unam-transients/tequila/hardware/Edmund Optics/39038/curv_39038.pdf

## 550 - 750nm, λ/4 Achromatic Waveplate Typical Retardance

## FOR REFERENCE ONLY

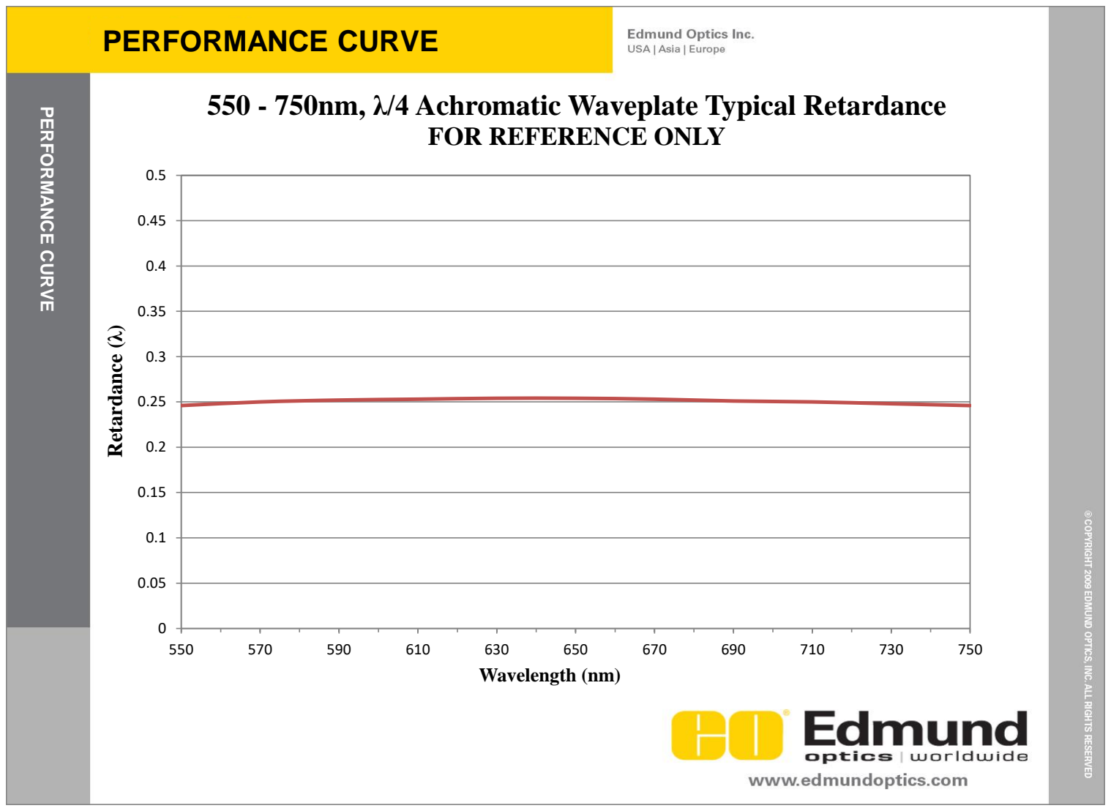
[picture p2: page 1]

0

0.05

0.1

0.15

0.2

0.25

0.3

0.35

0.4

0.45

0.5

550 | 570 | 590 | 610 | 630 | 650 | 670 | 690 | 710 | 730 | 750

Retardance (

λ)

Wavelength (nm)

PERFORMANCE CURVE

# PERFORMANCE CURVE
