unam-transients/tequila/hardware/Edmund Optics/39039/curv_39039.pdf

## 550 - 750nm, λ/2 Achromatic Waveplate Typical Retardance

## FOR REFERENCE ONLY

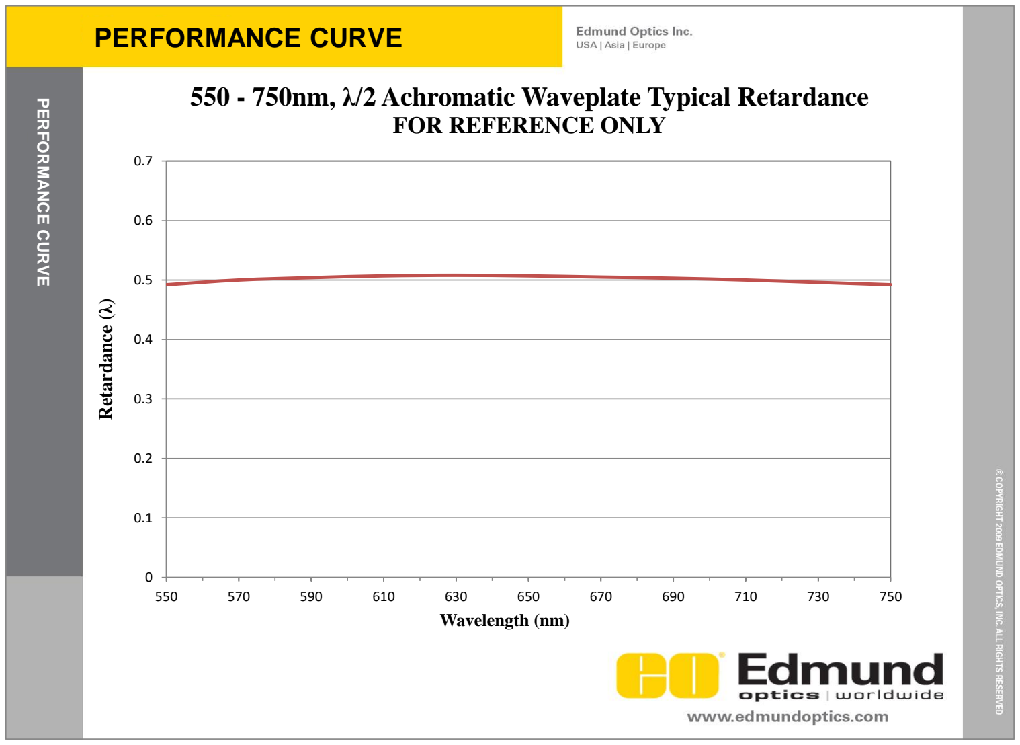
[picture p3: page 1]

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
550 | 570 | 590 | 610 | 630 | 650 | 670 | 690 | 710 | 730 | 750

Retardance (

λ)

Wavelength (nm)

PERFORMANCE CURVE

# PERFORMANCE CURVE
