unam-transients/tequila/hardware/Edmund Optics/63765/spec_63765.pdf

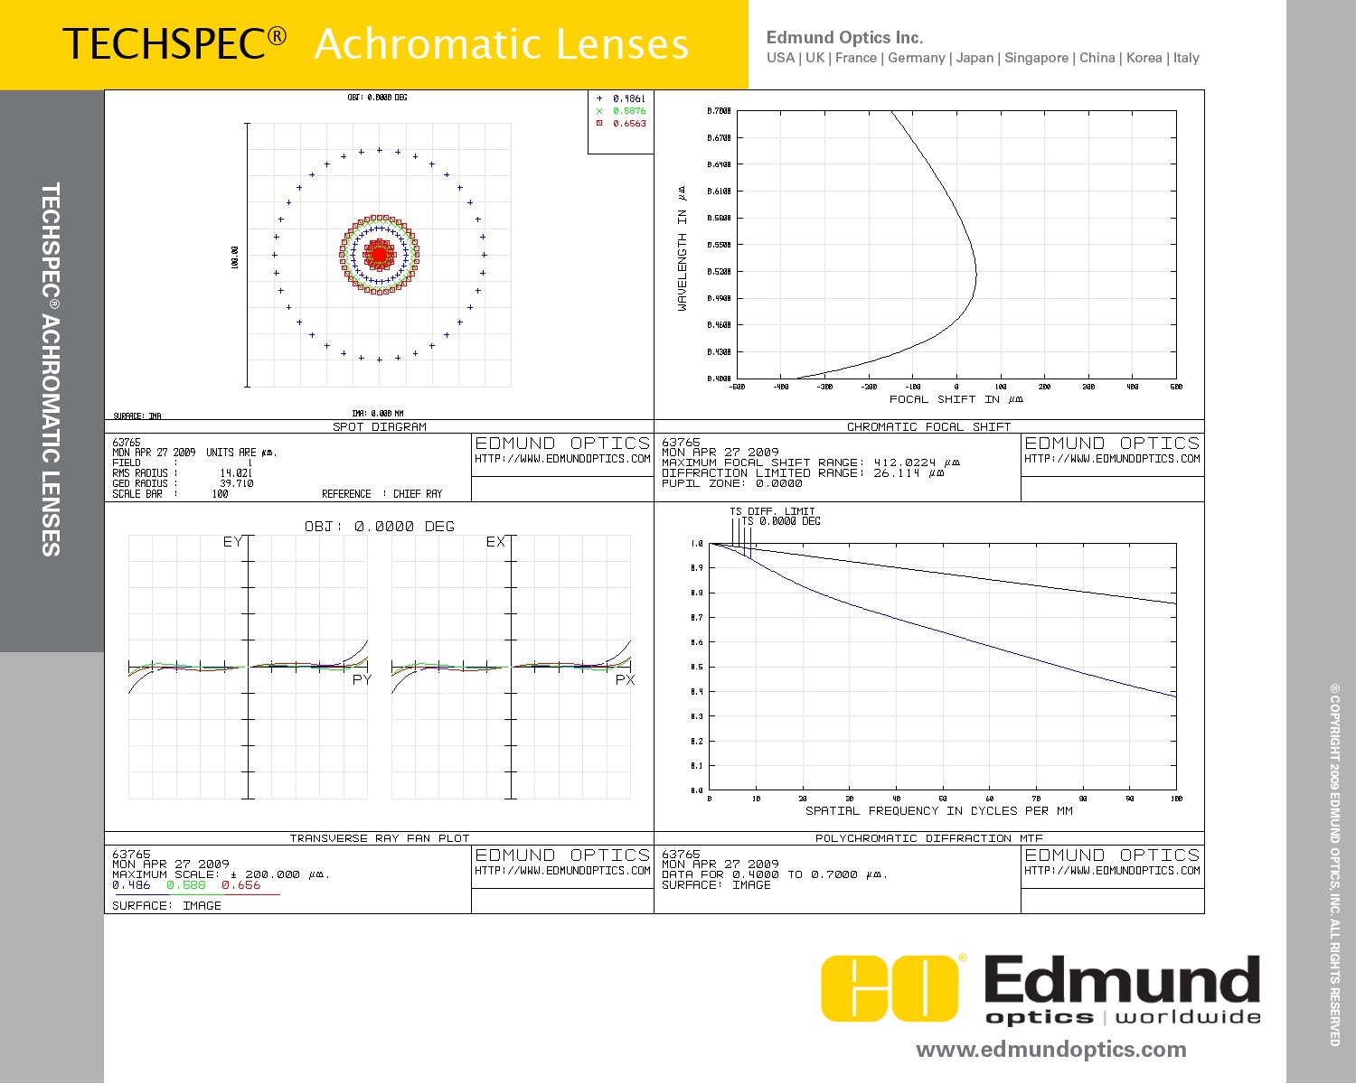
[picture p13: page 1]
