unam-transients/tequila/hardware/Edmund Optics/11147/prnt_11147.pdf

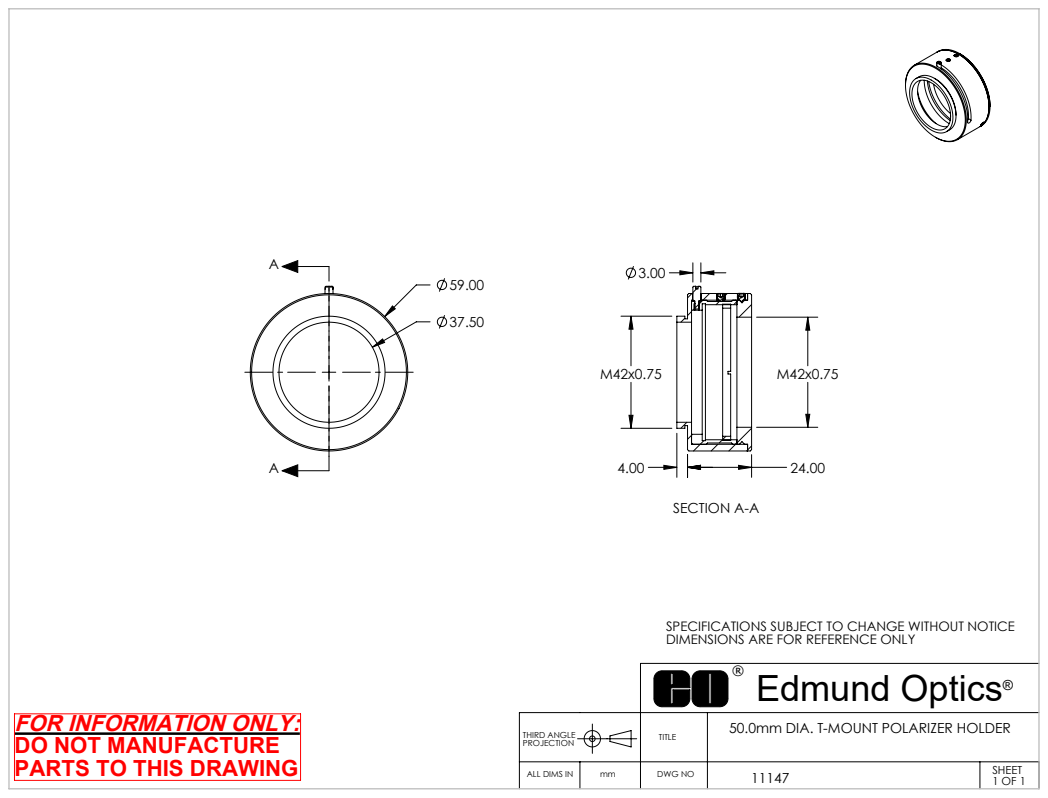
[picture p62: page 1]
THIRD ANGLE; SECTION A-A; DWG NO; 1 OF 1 ALL DIMS IN

SPECIFICATIONS SUBJECT TO CHANGE WITHOUT NOTICE
DIMENSIONS ARE FOR REFERENCE ONLY
Edmund Optics®

FOR INFORMATION ONLY:
DO NOT MANUFACTURE
PARTS TO THIS DRAWING

50.0mm DIA. T-MOUNT POLARIZER HOLDER
