unam-transients/tequila/hardware/Edmund Optics/52294/PRNT_52294.pdf

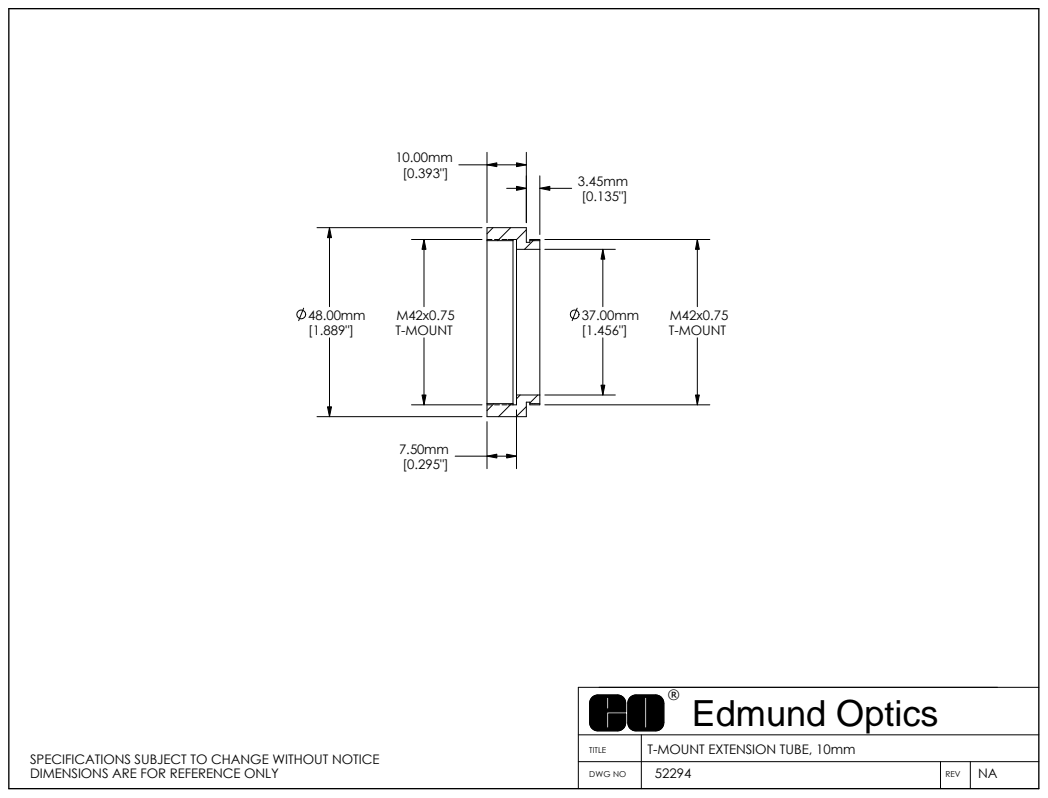
[picture p63: page 1]
T-MOUNT; Edmund Optics

TITLE | | | | T-MOUNT EXTENSION TUBE, 10mm

SPECIFICATIONS SUBJECT TO CHANGE WITHOUT NOTICE
DIMENSIONS ARE FOR REFERENCE ONLY

DWG NO | 52294 | REV | NA
