unam-transients/tequila/hardware/Edmund Optics/52304/prnt_52304.pdf

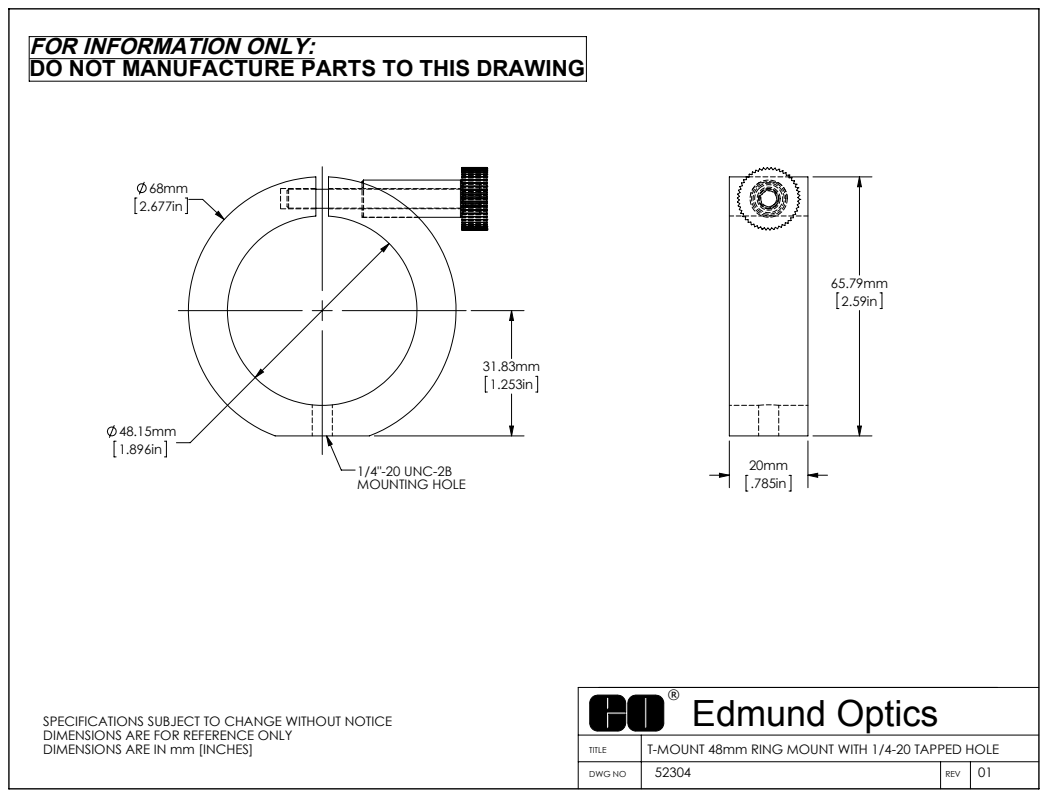
[picture p64: page 1]
1/4"-20 UNC-2B MOUNTING HOLE; Edmund Optics ®

FOR INFORMATION ONLY:
DO NOT MANUFACTURE PARTS TO THIS DRAWING

SPECIFICATIONS SUBJECT TO CHANGE WITHOUT NOTICE
DIMENSIONS ARE FOR REFERENCE ONLY
DIMENSIONS ARE IN mm [INCHES]

TITLE | T-MOUNT 48mm RING MOUNT WITH 1/4-20 TAPPED HOLE
DWG NO | 52304 | REV | 01
