unam-transients/tequila/hardware/Edmund Optics/53231/PRNT_53231.pdf

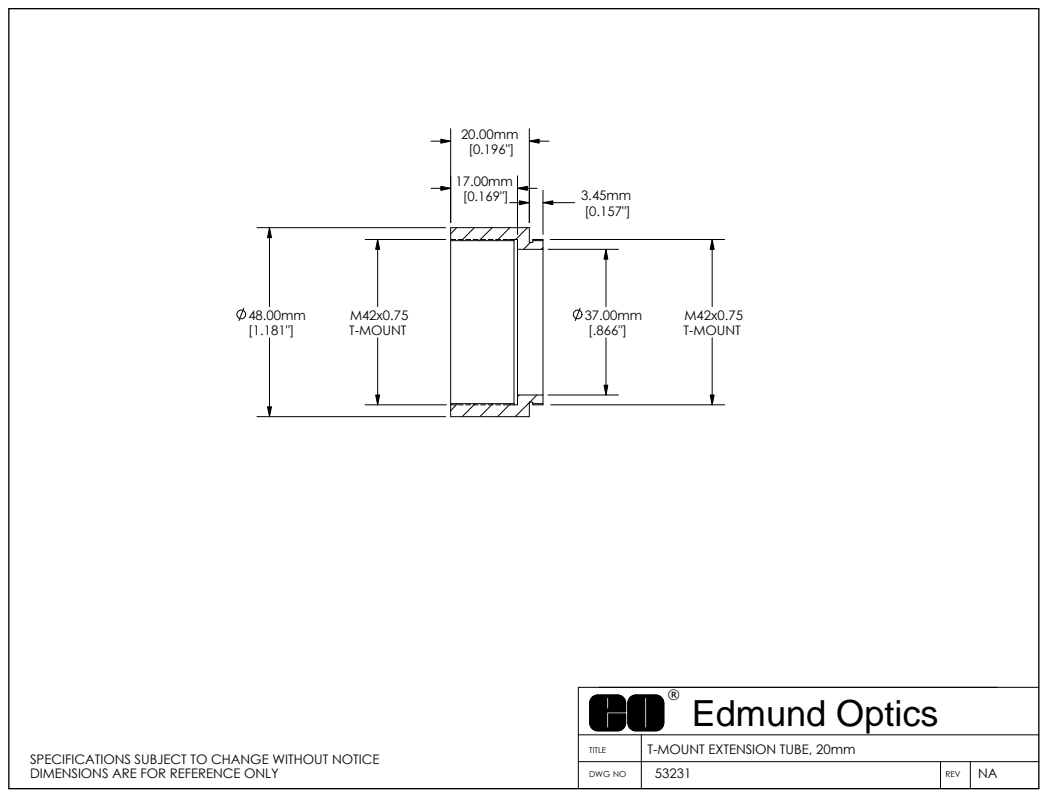
[picture p65: page 1]
Edmund Optics; T-MOUNT

TITLE | | | | T-MOUNT EXTENSION TUBE, 20mm

SPECIFICATIONS SUBJECT TO CHANGE WITHOUT NOTICE
DIMENSIONS ARE FOR REFERENCE ONLY

DWG NO | 53231 | REV | NA
