unam-transients/tequila/hardware/Edmund Optics/57978/prnt_57978.pdf

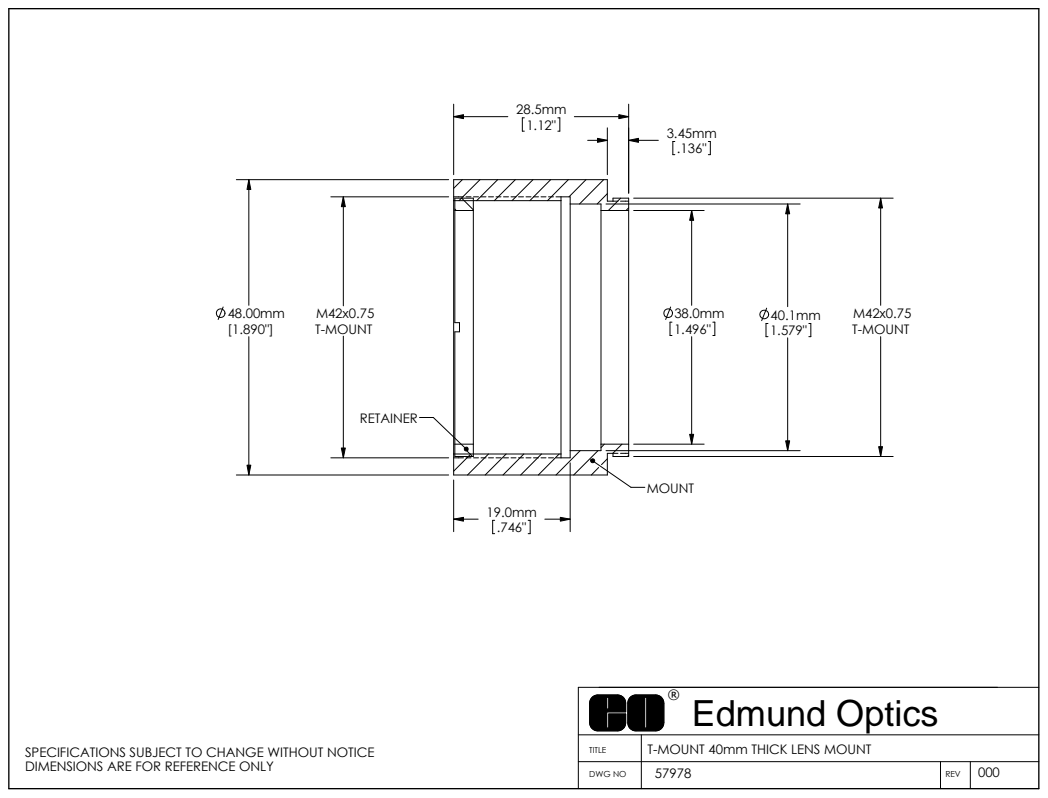
[picture p66: page 1]
T-MOUNT; MOUNT; RETAINER; DIMENSIONS ARE FOR REFERENCE ONLY; DWG NO; REV; Edmund Optics

SPECIFICATIONS SUBJECT TO CHANGE WITHOUT NOTICE

TITLE | | | T-MOUNT 40mm THICK LENS MOUNT
