unam-transients/tequila/hardware/Edmund Optics/58735/PRNT_58735.pdf

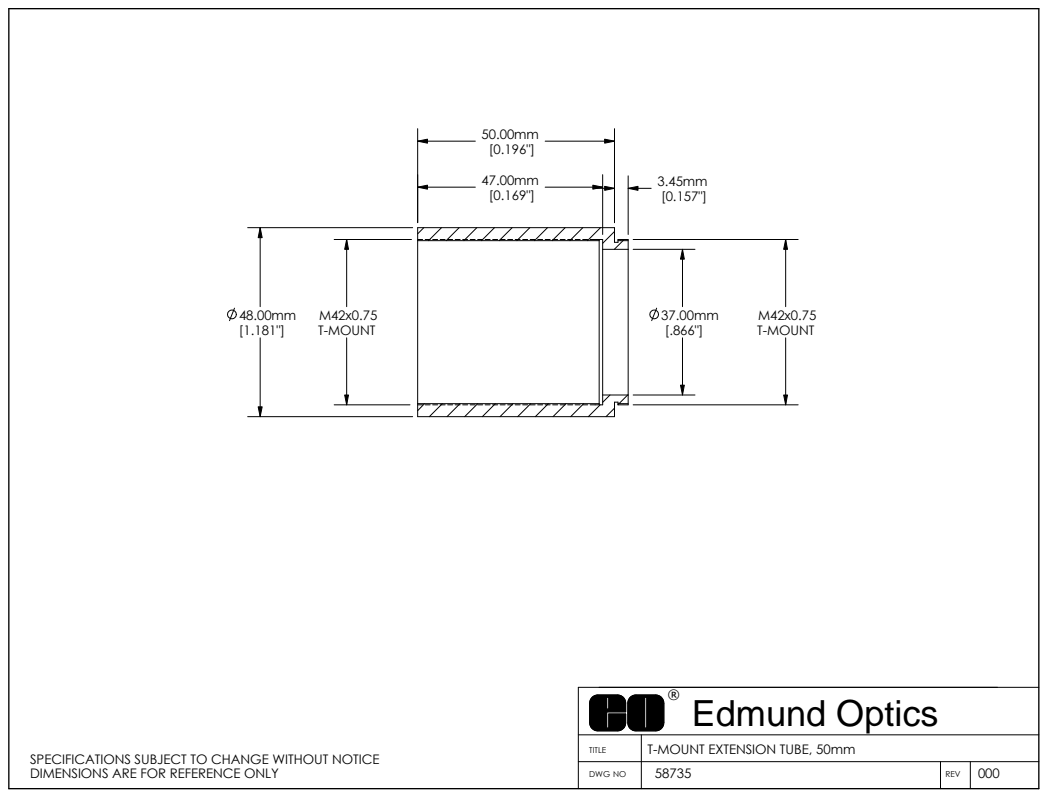
[picture p67: page 1]
Edmund Optics; T-MOUNT

TITLE | | | T-MOUNT EXTENSION TUBE, 50mm
DWG NO | 58735 000 | REV

SPECIFICATIONS SUBJECT TO CHANGE WITHOUT NOTICE
DIMENSIONS ARE FOR REFERENCE ONLY
