unam-transients/tequila/hardware/Edmund Optics/66037/prnt_66037.pdf

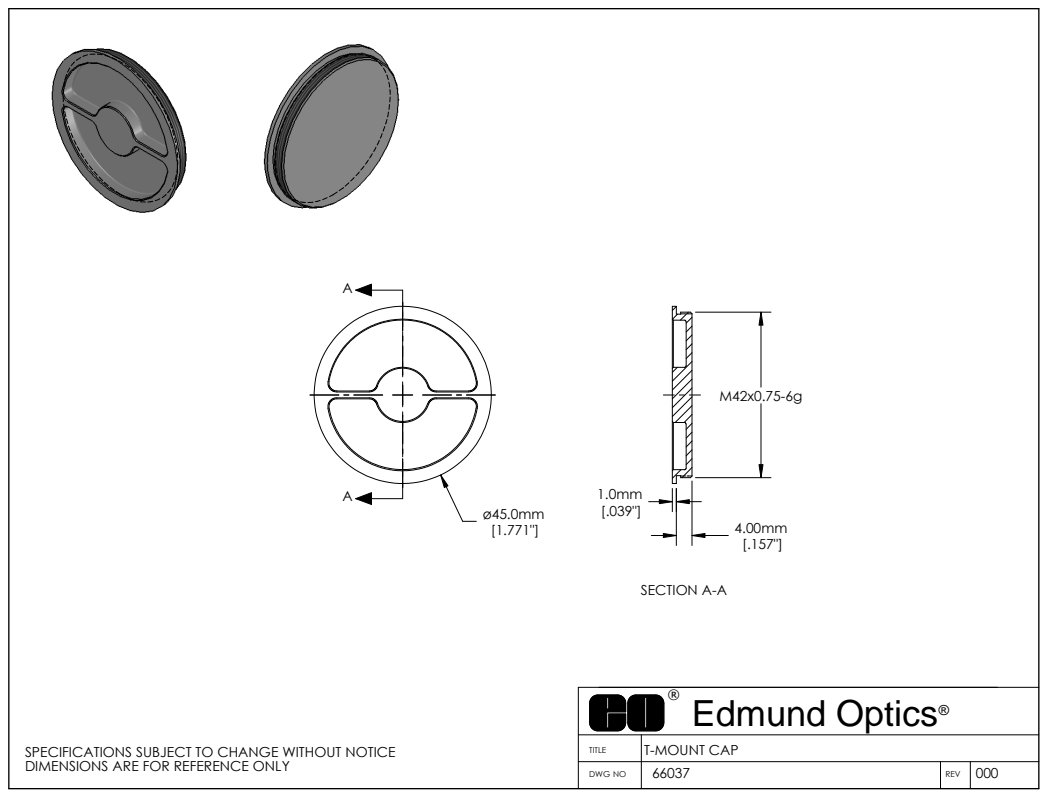
[picture p68: page 1]
SECTION A-A; DIMENSIONS ARE FOR REFERENCE ONLY; DWG NO; REV; Edmund Optics®

TITLE SPECIFICATIONS SUBJECT TO CHANGE WITHOUT NOTICE

T-MOUNT CAP
66037 000
