unam-transients/tequila/hardware/HWP Adapter/2025-06-24 Conceptual Design.jpg

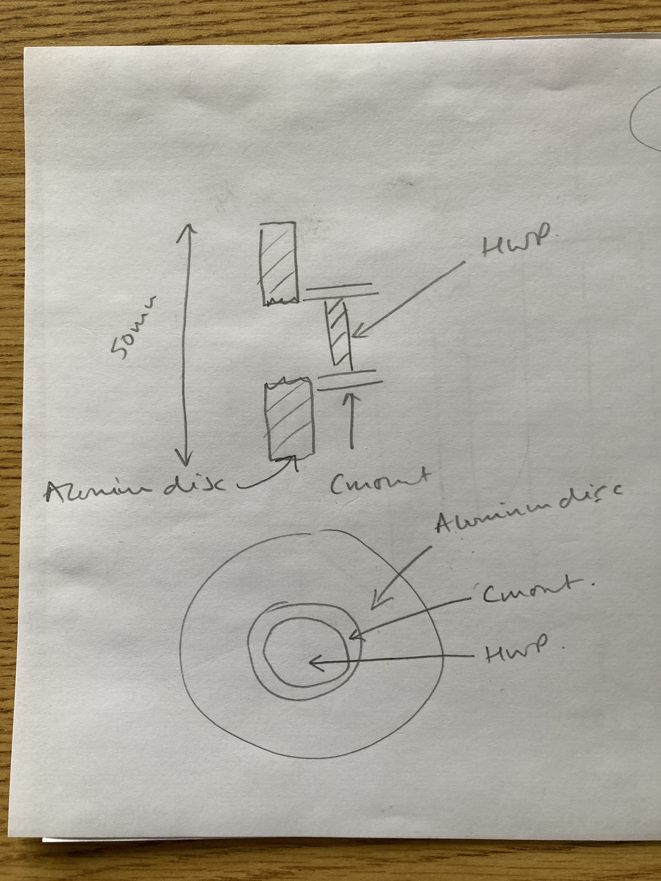
hardware/HWP Adapter/2025-06-24 Conceptual Design.jpg
